moduloindustries/thinkeys/23.gif

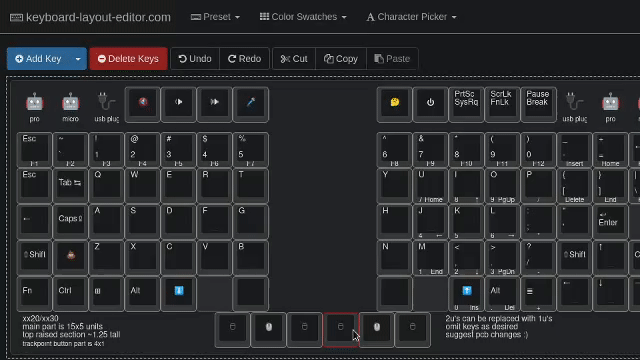
23.gif
