moduloindustries/thinkeys/23.png

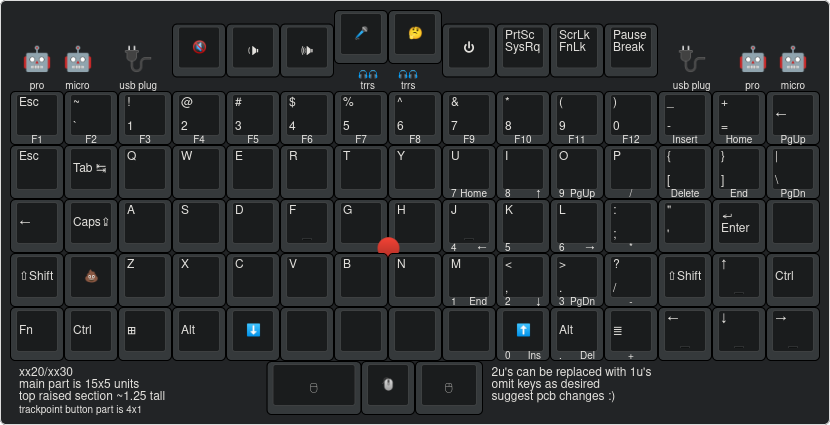
23.png
